IowaScaledEngineering/i2c-relay16/pg/i2c-relay16-v2.0-d9f09d9/i2c-relay16-pcb.pdf

# i2c-relay16.pcb

# 1. Table of Contents (This Page) Created on Fri Mar 3 21:47:10 2017

# 2. component 3. solder 4. outline 5. plated-drill 6. componentmask 7. soldermask 8. topsilk 9. bottomsilk 10. toppaste 11. topassembly 12. bottomassembly 13. fab

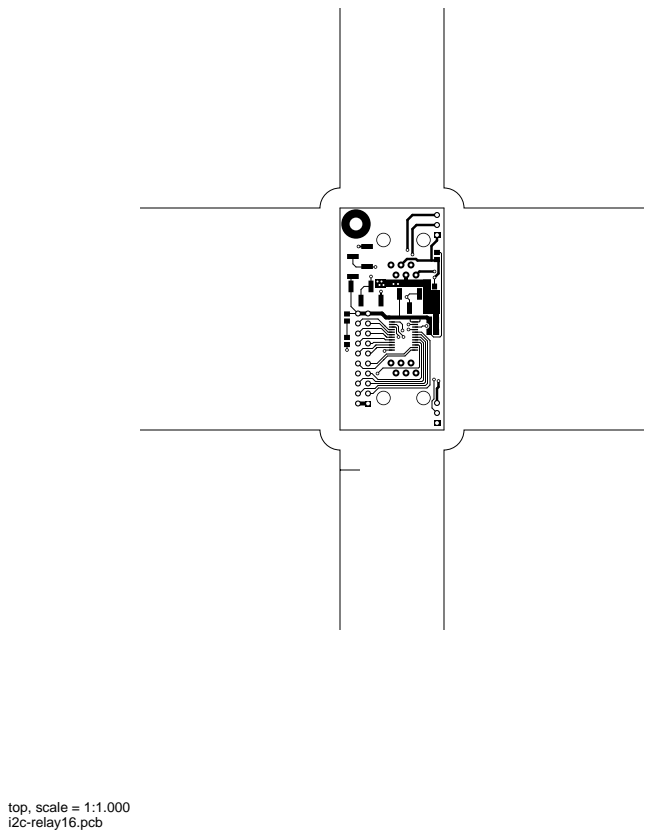
[picture p59: page 2]
top, scale = 1:1.000


bottom (mirrored), scale = 1:1.000

outline, scale = 1:1.000


plated-drill, scale = 1:1.000

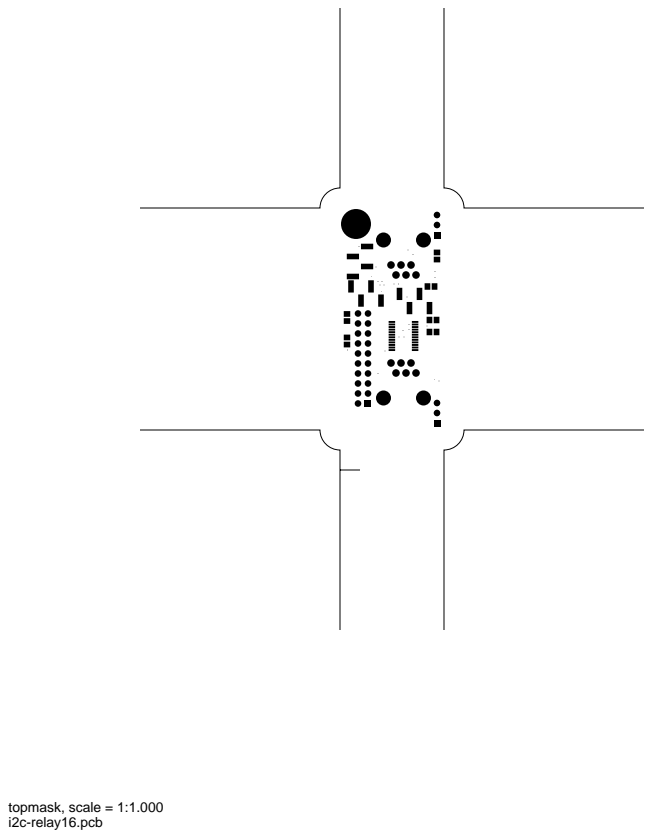
[picture p60: page 6]
topmask, scale = 1:1.000


bottommask (mirrored), scale = 1:1.000

topsilk, scale = 1:1.000

bottomsilk (mirrored), scale = 1:1.000

toppaste, scale = 1:1.000

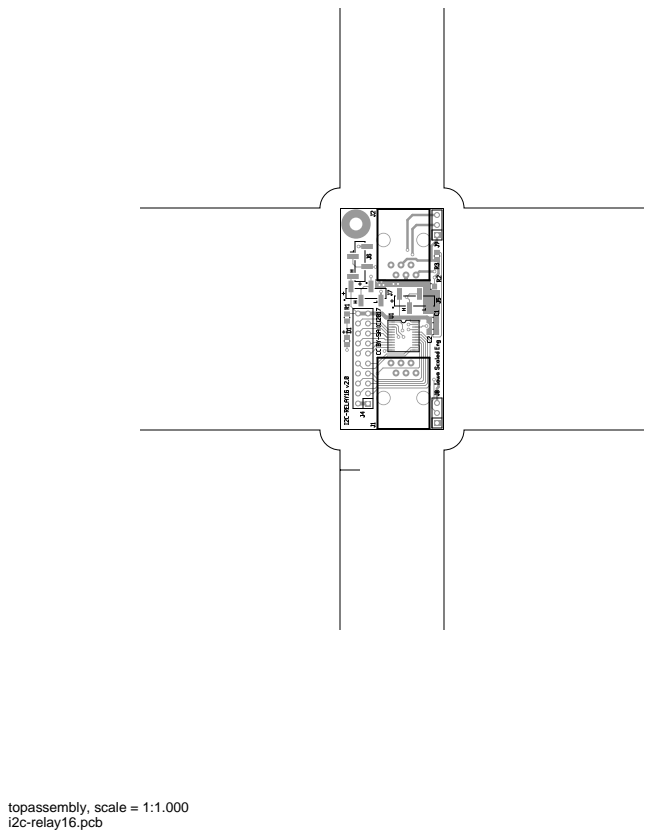
[picture p61: page 11]
topassembly, scale = 1:1.000


bottomassembly (mirrored), scale = 1:1.000

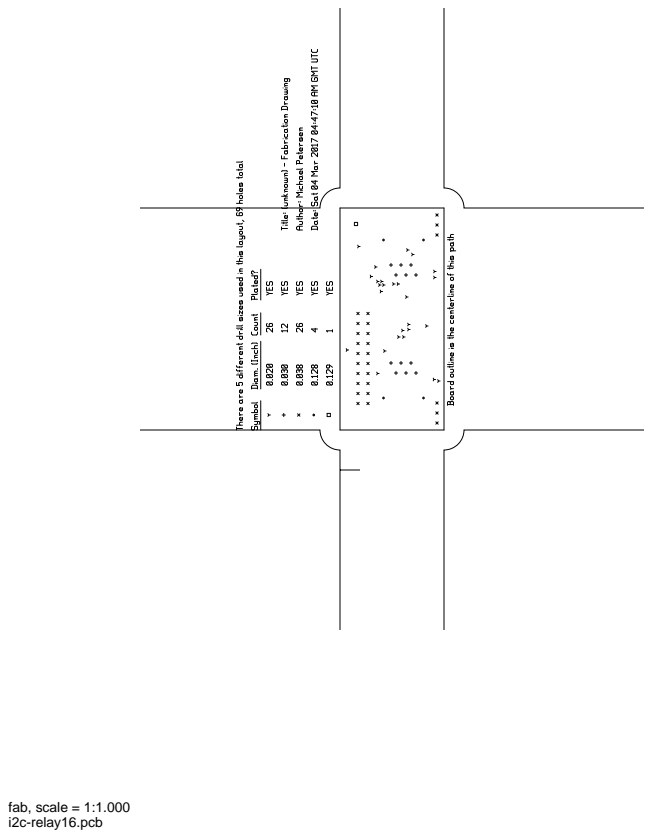
[picture p62: page 13]
fab, scale = 1:1.000
