IowaScaledEngineering/i2c-relay16/pg/i2c-relay16-v1.1-26de41d/i2c-relay16-pcb.pdf

# i2c-relay16.pcb

# 1. Table of Contents (This Page) Created on Mon Feb 2 11:09:46 2015

# 2. component 3. solder 4. outline 5. plated-drill 6. componentmask 7. soldermask 8. topsilk 9. bottomsilk 10. toppaste 11. topassembly 12. bottomassembly 13. fab

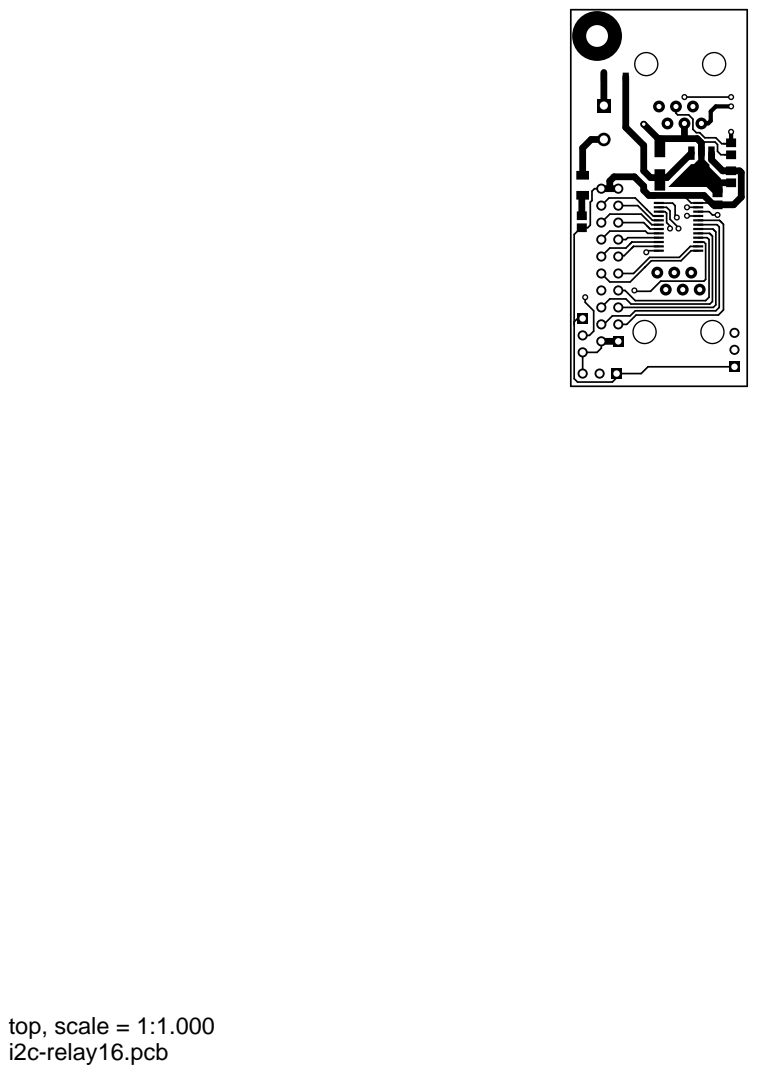
[picture p72: page 2]
top, scale = 1:1.000

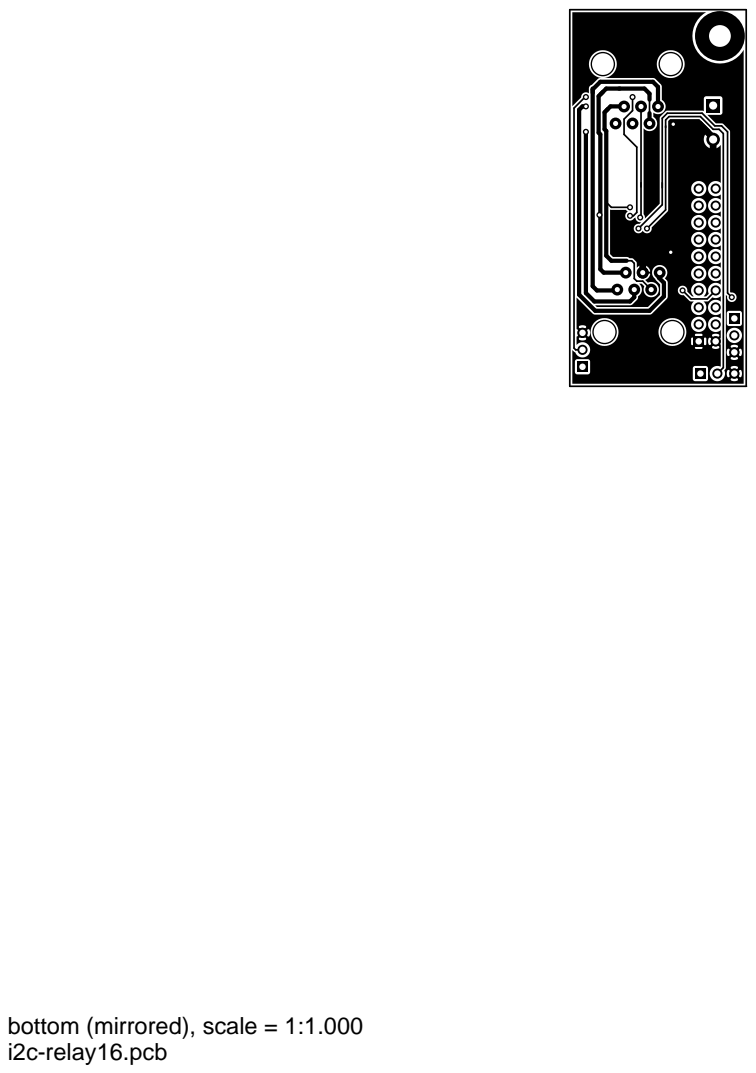
[picture p73: page 3]

bottom (mirrored), scale = 1:1.000

outline, scale = 1:1.000

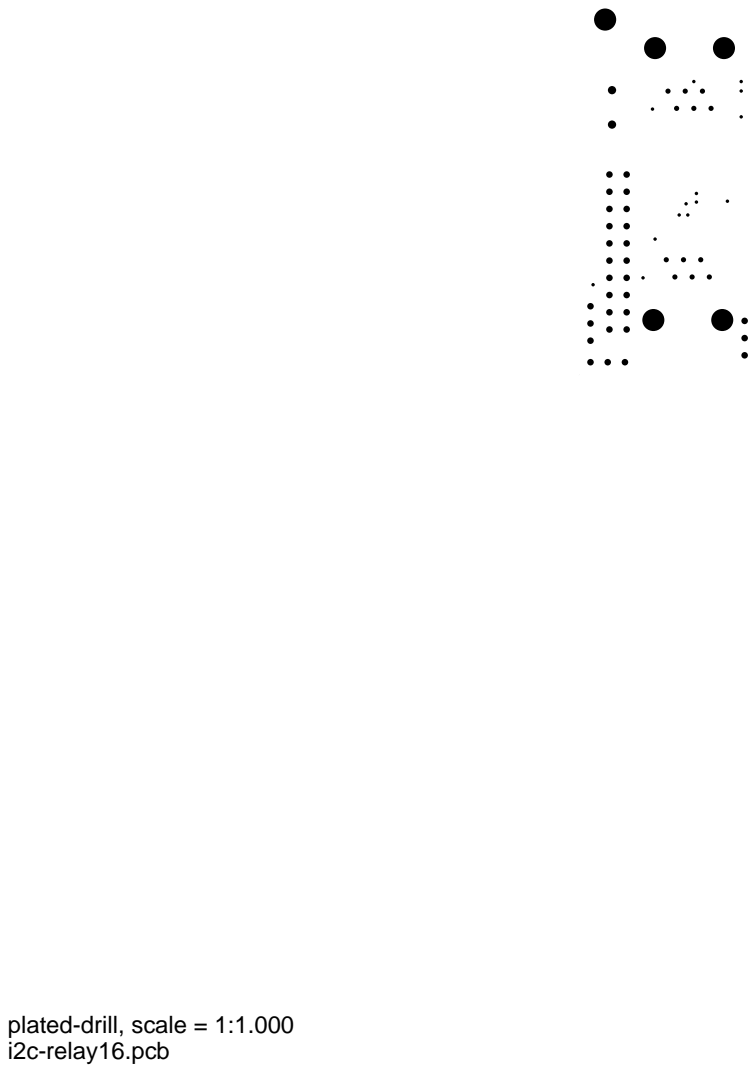
[picture p74: page 5]

plated-drill, scale = 1:1.000

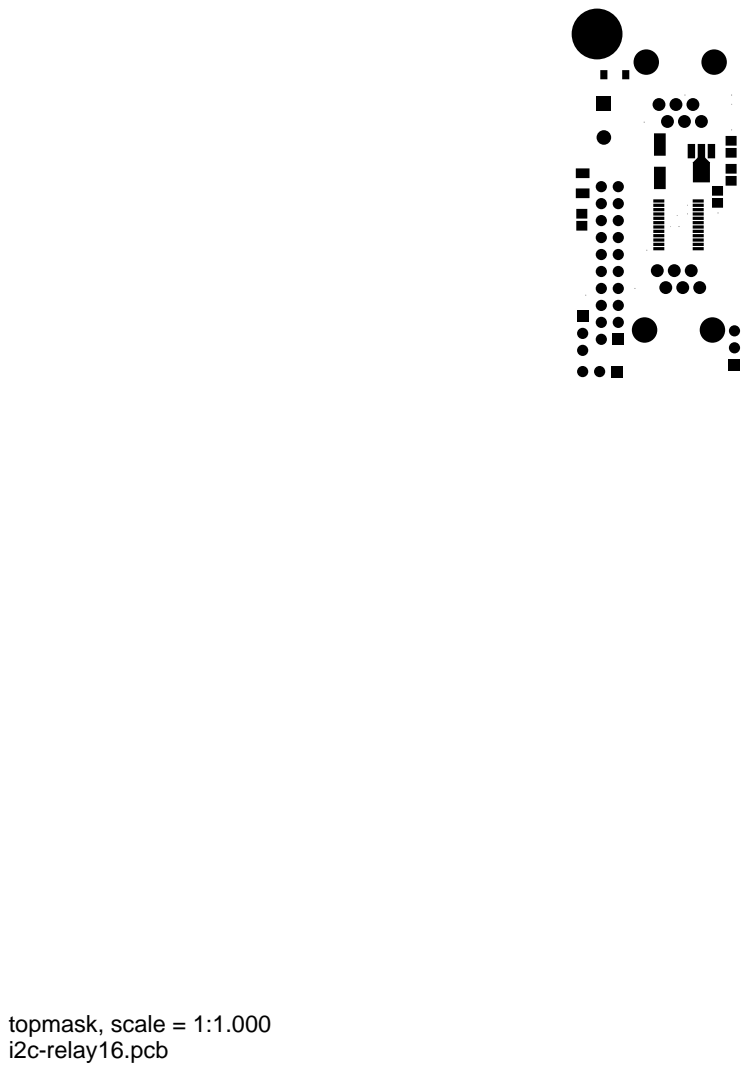
[picture p75: page 6]
topmask, scale = 1:1.000

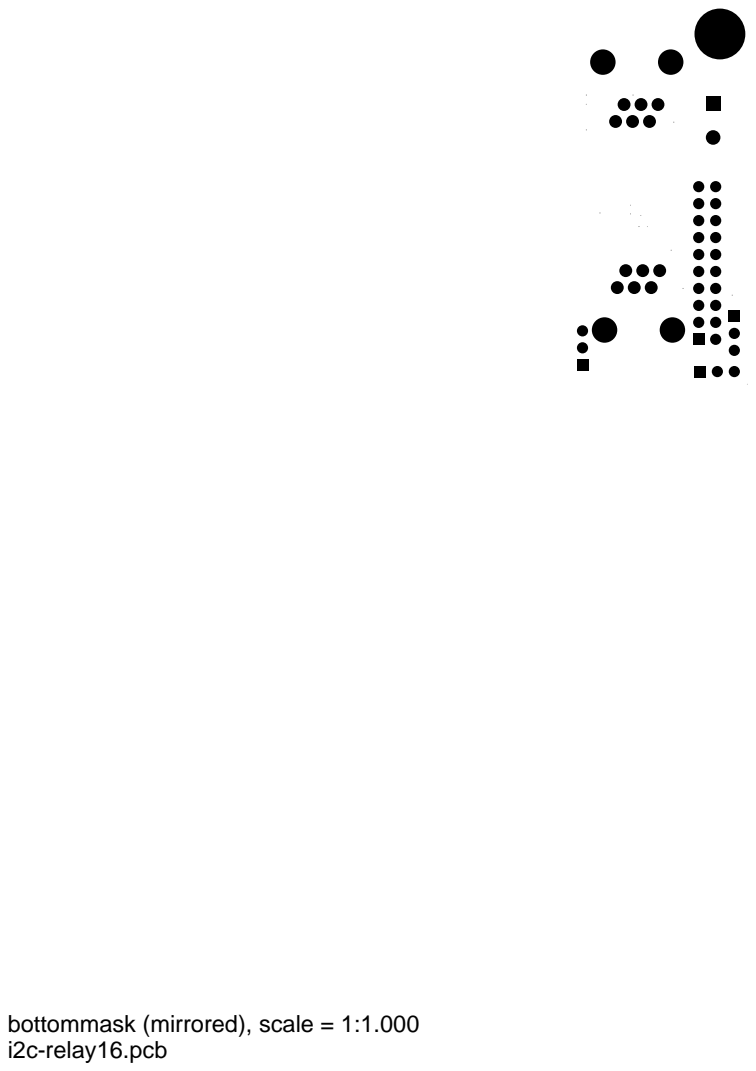
[picture p76: page 7]

bottommask (mirrored), scale = 1:1.000

topsilk, scale = 1:1.000 bottomsilk (mirrored), scale = 1:1.000

toppaste, scale = 1:1.000

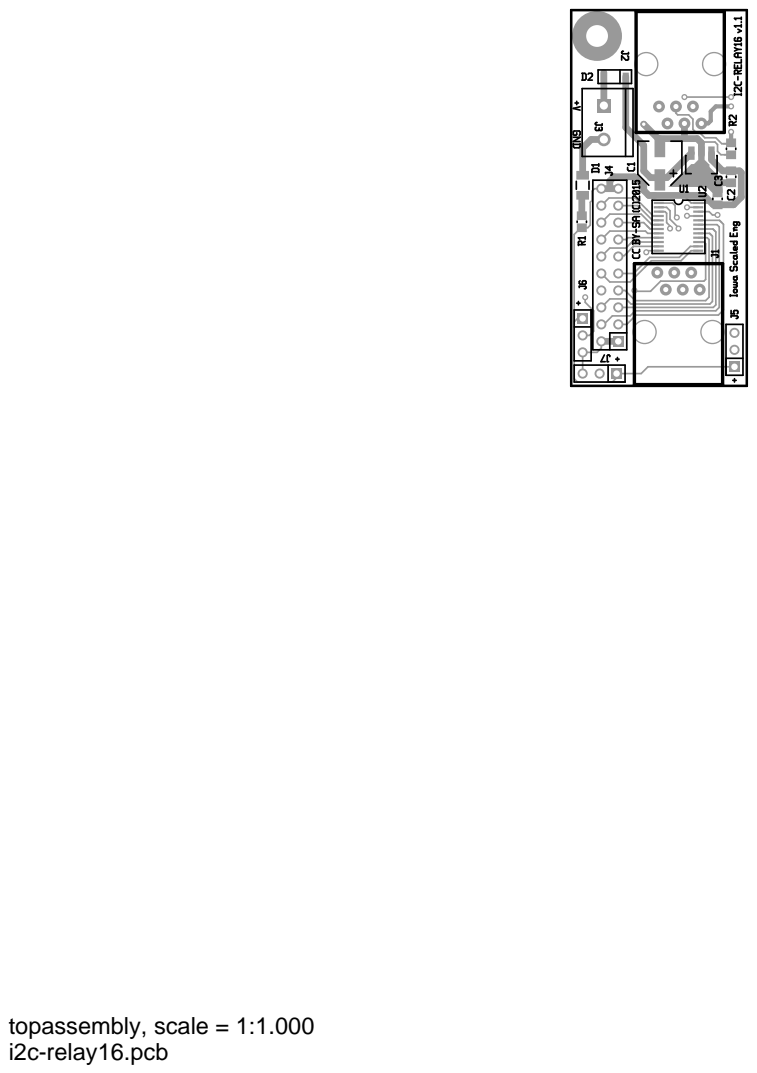
[picture p77: page 11]
topassembly, scale = 1:1.000

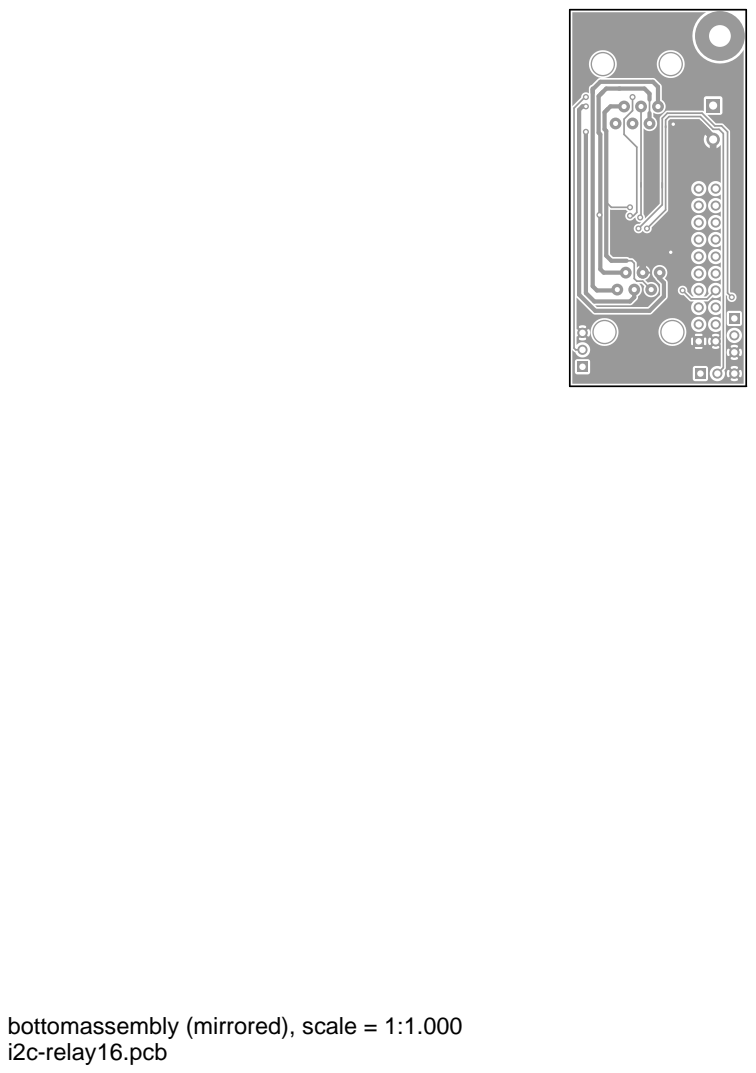
[picture p78: page 12]

bottomassembly (mirrored), scale = 1:1.000

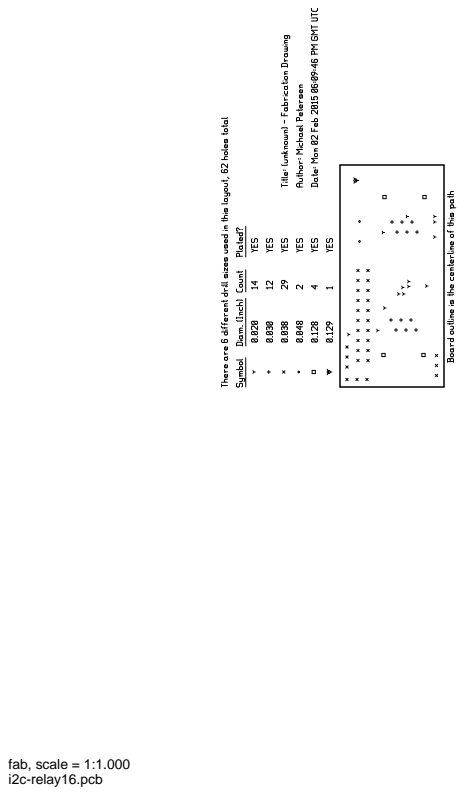
[picture p79: page 13]
fab, scale = 1:1.000
