IowaScaledEngineering/i2c-relay16/pg/i2c-relay16-v2.0-d9f09d9/i2c-relay16.pdf

*Jack as viewed from front

5 5 SCL

/INT 6
