IowaScaledEngineering/i2c-relay16/pg/i2c-relay16-v1.2-4fc73de/i2c-relay16.pdf

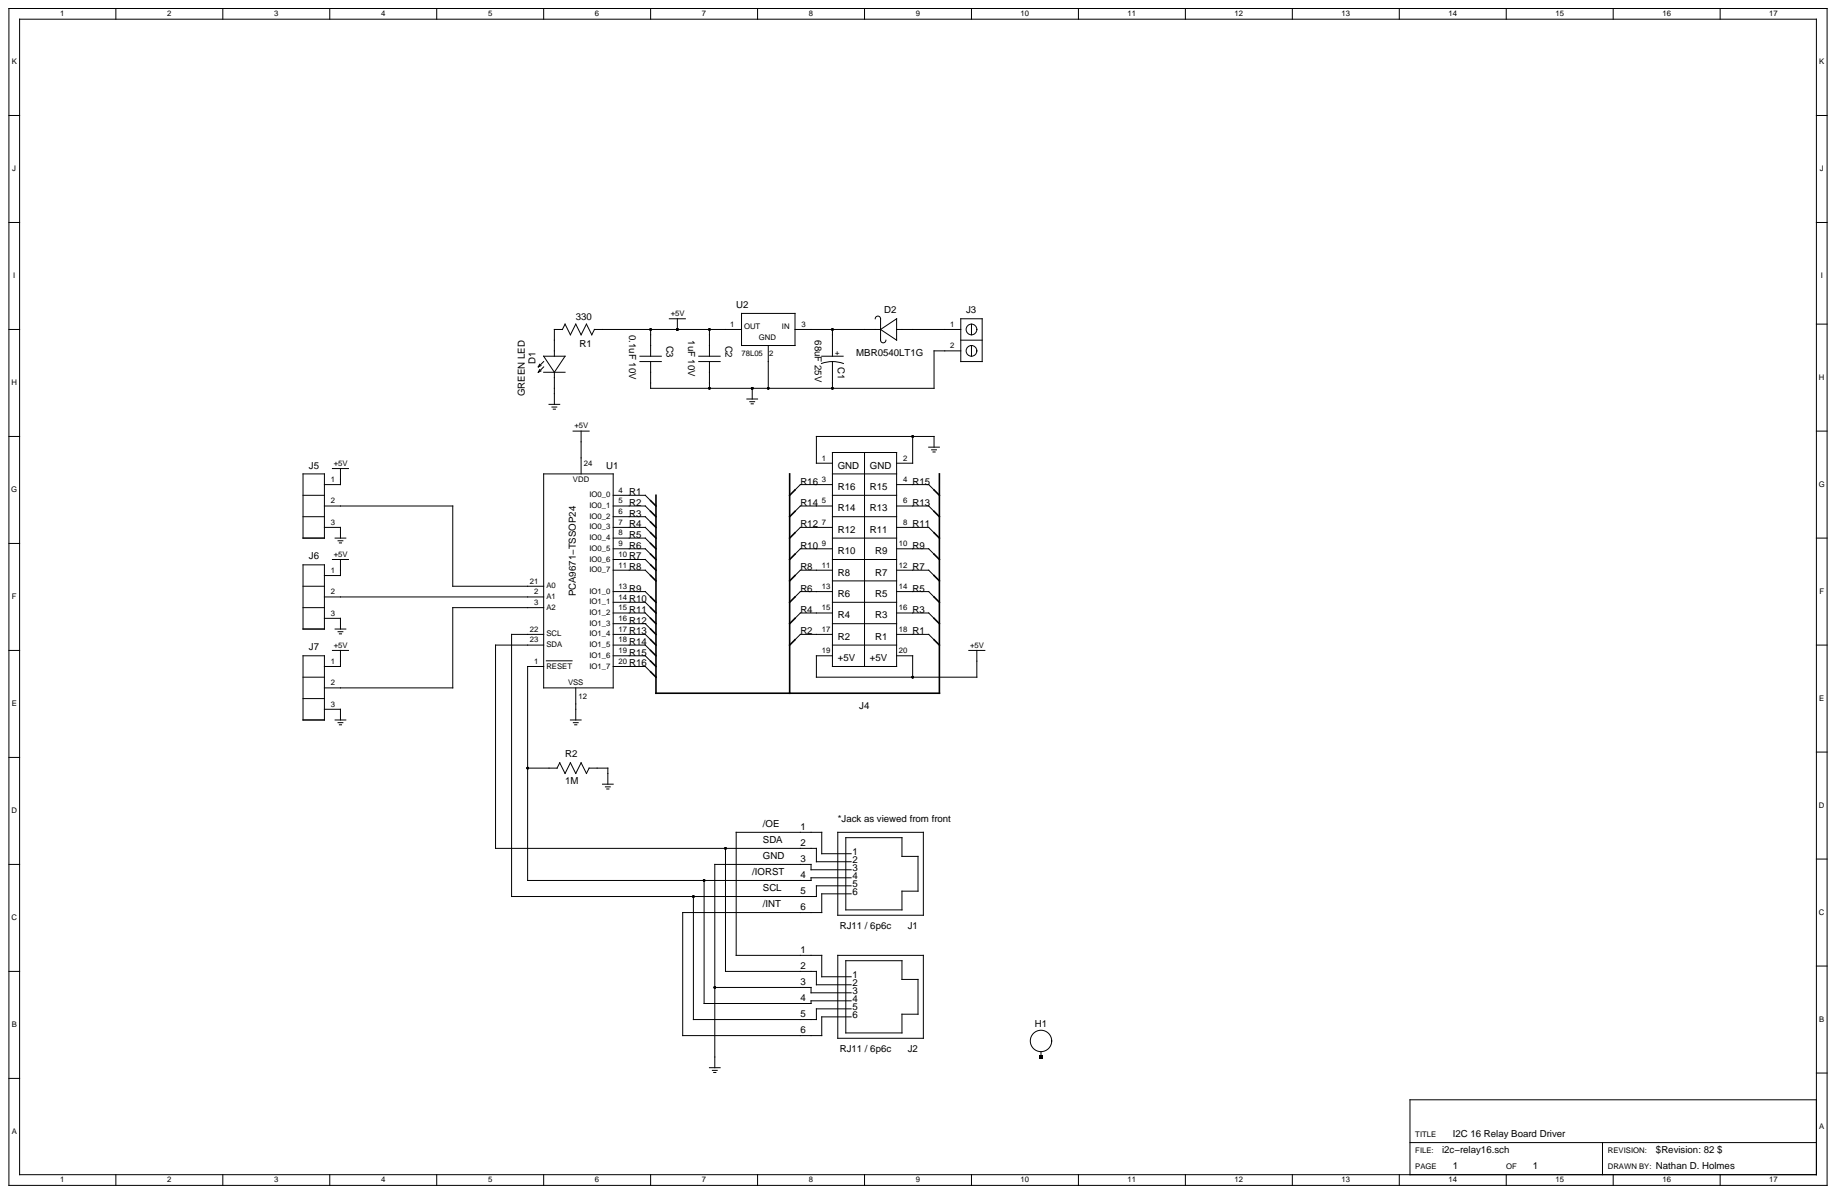
[picture p82: page 1]

*Jack as viewed from front
