IowaScaledEngineering/i2c-relay16/pg/i2c-relay16-v1.1-26de41d/i2c-relay16.pdf

*Jack as viewed from front
